Franzininho/franzininho-diy-board/Franzininho DIY/imagens/Franzininho-3D-2.png

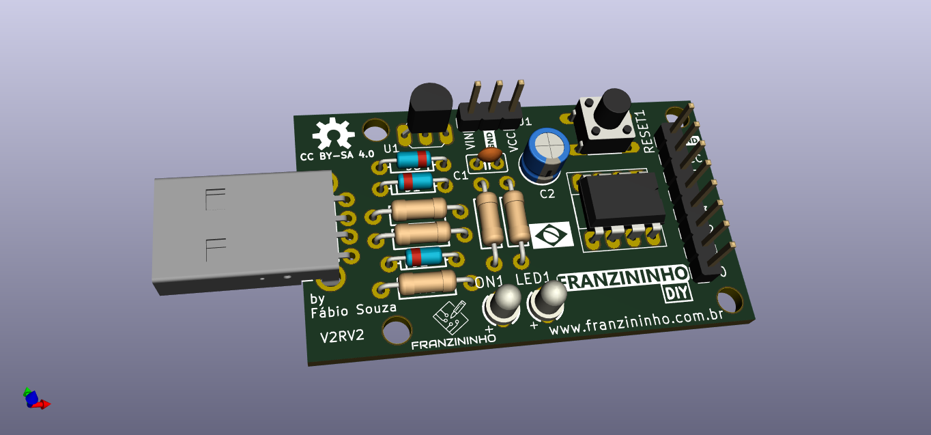
Franzininho DIY/imagens/Franzininho-3D-2.png
